xcezz/swh17_tamagotchi/code/main/anim.h

static const uint8_t PROGMEM
eyes1_bmp[] =
{ B00111100,
  B01111110,
  B11111111,
  B11100011,
  B11100011,
  B11100011,
  B01111110,
  B00111100
},
eyes2_bmp[] =
{ B00111100,
  B01100010,
  B11100011,
  B11100011,
  B11111111,
  B11111111,
  B01111110,
  B00111100
},
eyes3_bmp[] =
{ B00111100,
  B01111110,
  B11111111,
  B11111111,
  B11100011,
  B11100011,
  B01100010,
  B00111100
},
eyes4_bmp[] =
{ B00111100,
  B01000110,
  B11000111,
  B11000111,
  B11111111,
  B11111111,
  B01111110,
  B00111100
},
eyes5_bmp[] =
{ B00111100,
  B01111110,
  B10001111,
  B10001111,
  B10001111,
  B11111111,
  B01111110,
  B00111100
},
eyes6_bmp[] =
{ B00111100,
  B01111110,
  B11110001,
  B11110001,
  B11110001,
  B11111111,
  B01111110,
  B00111100
},
eyes7_bmp[] =
{ B00111100,
  B01000110,
  B11000111,
  B11000111,
  B11111111,
  B11111111,
  B01111110,
  B00111100
},
eyes8_bmp[] =
{ B00111100,
  B01111110,
  B11111111,
  B11111111,
  B11000111,
  B11000111,
  B01000110,
  B00111100
},
eyes9_bmp[] =
{ B00111100,
  B01111110,
  B11111111,
  B11111111,
  B11100011,
  B11100011,
  B01100010,
  B00111100
},
eyesclosed_bmp[] =
{ B00000000,
  B00000000,
  B00000000,
  B00000000,
  B00000000,
  B11000011,
  B01100110,
  B00111100
},
dead_bmp[] =
{ B01000001,
  B00100010,
  B00010100,
  B00001000,
  B00010100,
  B00100010,
  B01000001,
  B00000000
},
angry3_right_bmp[] =
{ B01110000,
  B11111000,
  B11111100,
  B11100110,
  B11100111,
  B11100111,
  B01111110,
  B00111100
},
angry3_left_bmp[] =
{ B00001110,
  B00011111,
  B00111111,
  B01100111,
  B11100111,
  B11100111,
  B01111110,
  B00111100
},
angry1_right_bmp[] =
{ B01111000,
  B11111100,
  B11100110,
  B11100111,
  B11100111,
  B11111111,
  B11111111,
  B01111110
},
angry1_left_bmp[] =
{ B00011110,
  B00111111,
  B01100111,
  B11100111,
  B11100111,
  B11111111,
  B11111111,
  B01111110
},
angry2_right_bmp[] =
{ B01110000,
  B11111000,
  B11100100,
  B11100110,
  B11100111,
  B11111111,
  B11111111,
  B01111110
},
angry2_left_bmp[] =
{ B00001110,
  B00011111,
  B00100111,
  B01100111,
  B11100111,
  B11111111,
  B11111111,
  B01111110
},
sleepy_bmp[] =
{ B00000000,
  B00000000,
  B00000000,
  B00000000,
  B00000000,
  B11000011,
  B01100110,
  B00111100
},
sadface_bmp[] =
{ B00000000,
  B01100110,
  B01100110,
  B00000000,
  B00000000,
  B00111100,
  B01000010,
  B00000000
},
heart_big_bmp[] =
{ B01100110,
  B11111111,
  B11111111,
  B11111111,
  B11111111,
  B01111110,
  B00111100,
  B00011000
},
heart_small_bmp[] =
{ B00000000,
  B01100110,
  B11111111,
  B11111111,
  B01111110,
  B00111100,
  B00011000,
  B00000000
};
